mohoyt/litl/img/litl2.jpeg

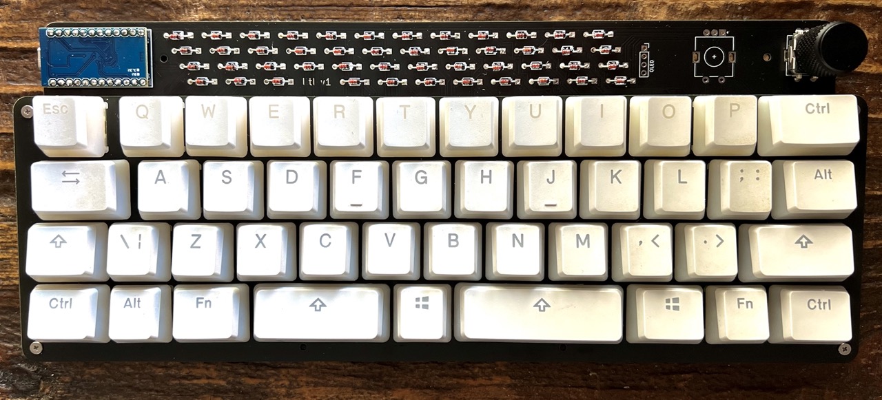
img/litl2.jpeg
