mohoyt/litl/img/litl_wpmhud.jpeg

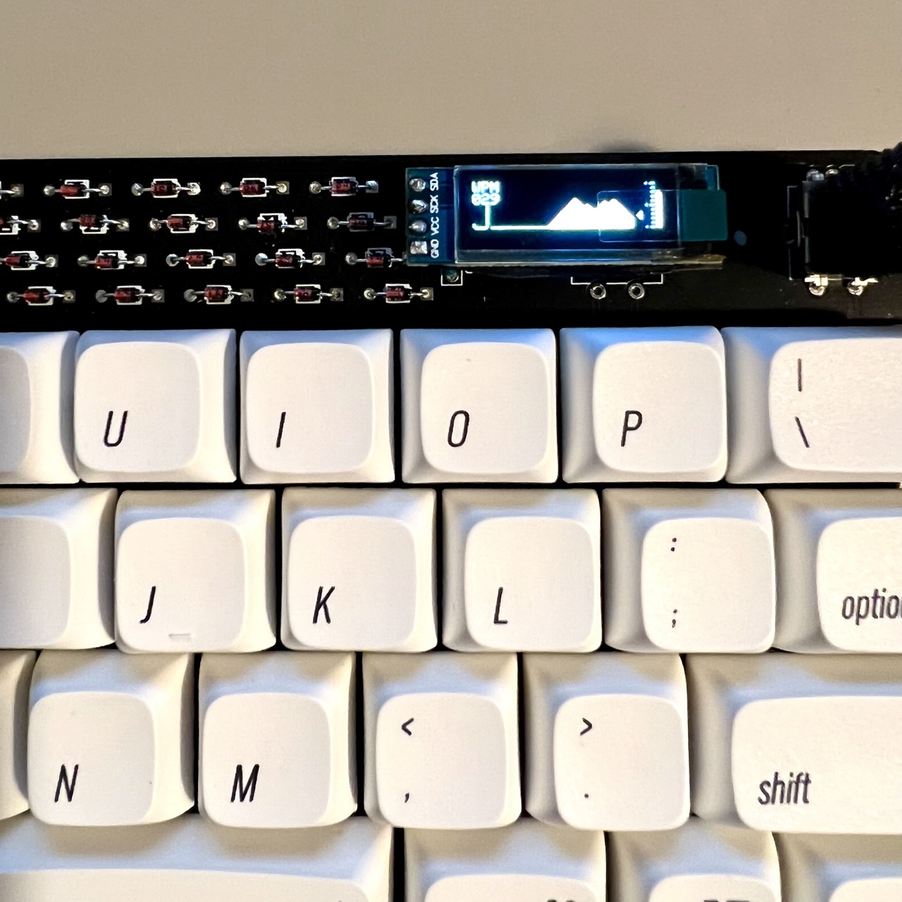
img/litl_wpmhud.jpeg
