mohoyt/litl/img/pcb_v1.png

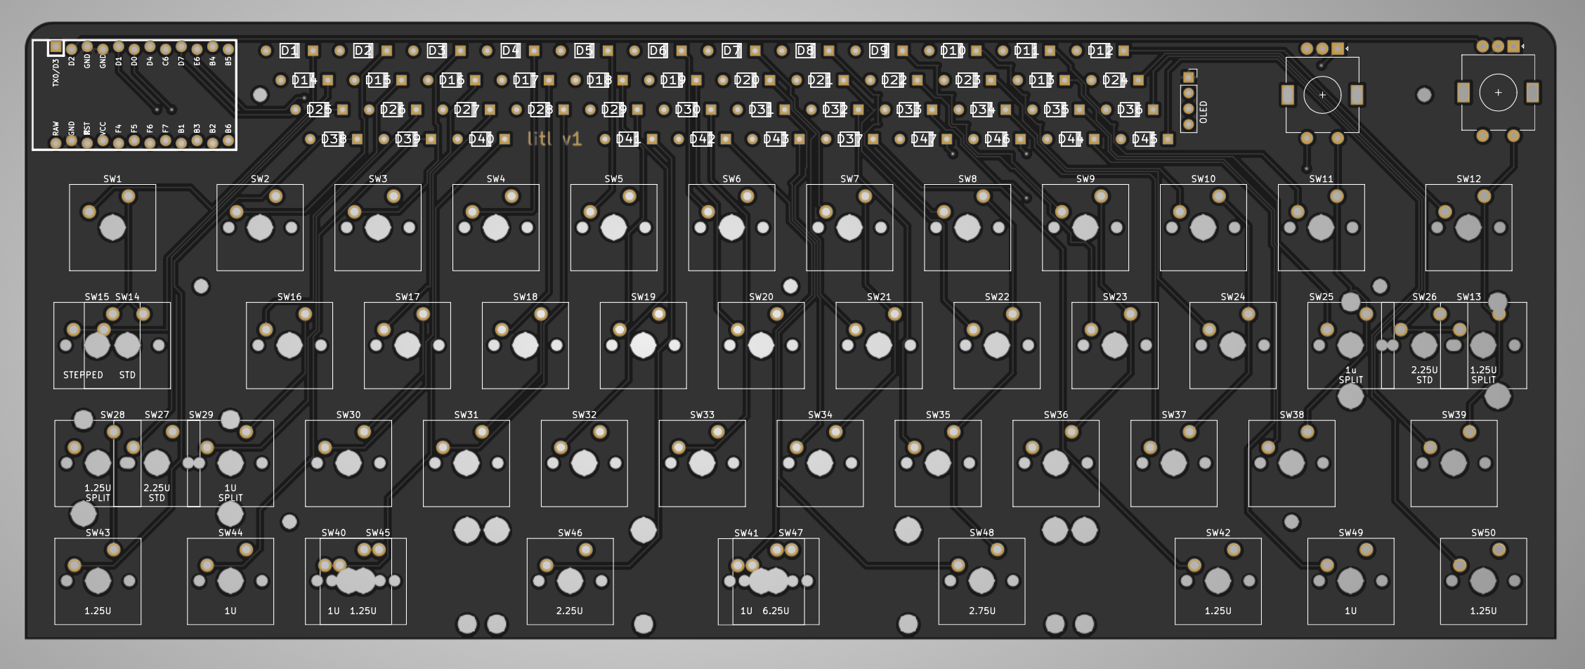
img/pcb_v1.png
