mohoyt/litl/PCB/Matrix layout.png

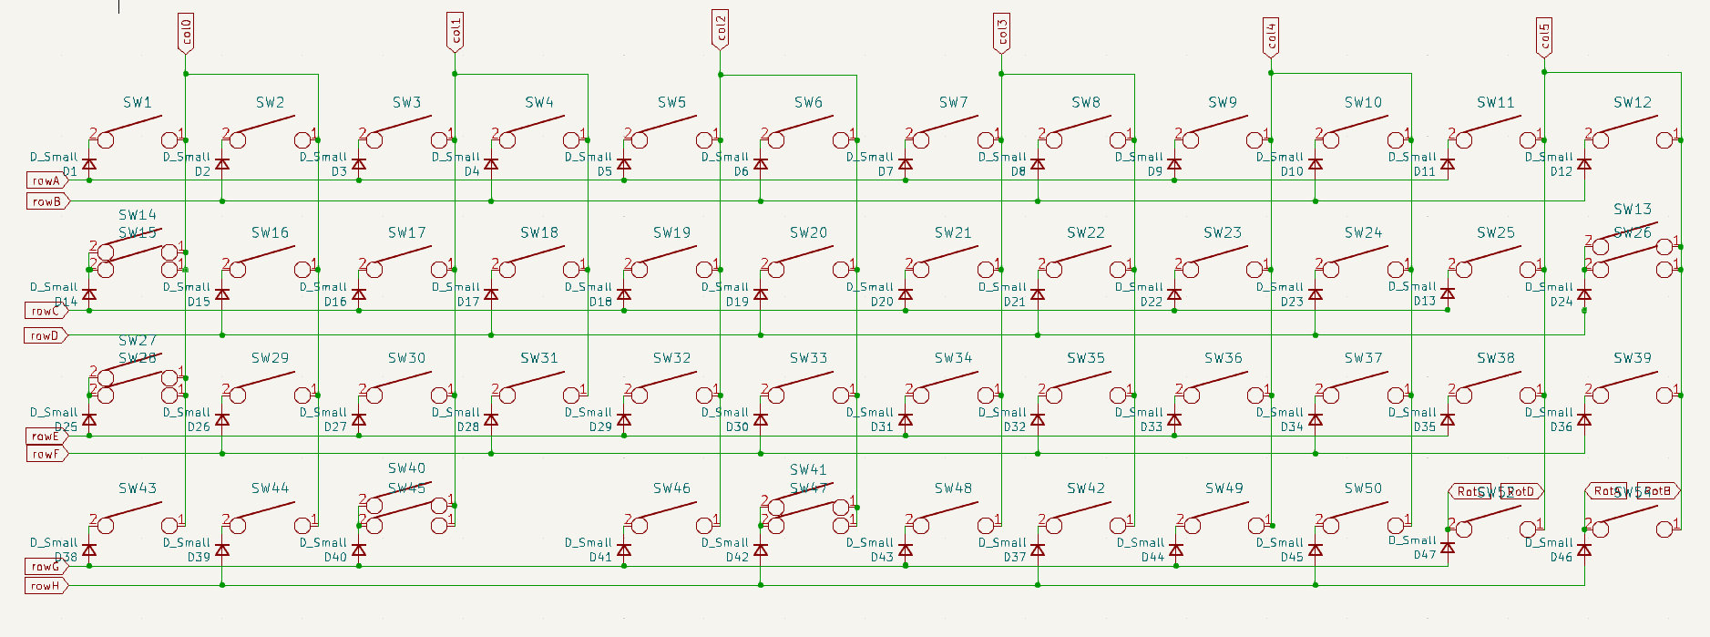
PCB/Matrix layout.png
