mohoyt/litl/firmware/QMK/litl/keymaps/bongocat/config.h

#pragma once

#define VIAL_KEYBOARD_UID {0x5C, 0x69, 0xA0, 0x59, 0xD3, 0x0D, 0xCF, 0x09}

#define VIAL_COMBO_ENTRIES 2
#define VIAL_KEY_OVERRIDE_ENTRIES 2
#define DYNAMIC_KEYMAP_LAYER_COUNT 3
#define VIAL_UNLOCK_COMBO_ROWS { 0, 7 }
#define VIAL_UNLOCK_COMBO_COLS { 0, 4 }
#define VIAL_ENCODER_DEFAULT { KC_VOLD, KC_VOLU, KC_MPRV, KC_MNXT, KC_TRNS, KC_TRNS }
